hqs1/EPD_clock/MCU_Project/BSP/EPD/imagedata.c

#include "imagedata.h"

const unsigned char INIT_IMAGE_DATA[] = 
{
0xFF,0xFF,0xFF,0xFF,0xFF,0xFF,0xFF,0xFF,0xFF,0xFF,0xFF,0xFF,0xFF,0xFF,0xFF,0xFF,
0xFF,0xFF,0xFF,0xFF,0xFF,0xFF,0xFF,0xFF,0xFF,0xFF,0xFF,0xFF,0xFF,0xFF,0xFF,0xFF,
0xFF,0xFF,0xFF,0xFF,0xFF,0xFF,0xFF,0xFF,0xFF,0xFF,0xFF,0xFF,0xFF,0xFF,0xFF,0xFF,
0xFF,0xFF,0xFF,0xFF,0xFF,0xFF,0xFF,0xFF,0xFF,0xFF,0xFF,0xFF,0xFF,0xFF,0xFF,0xFF,
0xFF,0xFF,0xFF,0xFF,0xFF,0xFF,0xFF,0xFF,0xFF,0xFF,0xFF,0xFF,0xFF,0xFF,0xFF,0xFF,
0xFF,0xFF,0xFF,0xFF,0xFF,0xFF,0xFF,0xFF,0xFF,0xFF,0xFF,0xFF,0xFF,0xFF,0xFF,0xFF,
0xFF,0xFF,0xFF,0xFF,0xFF,0xFF,0xFF,0xFF,0xFF,0xFF,0xFF,0xFF,0xFF,0xFF,0xFF,0xFF,
0xFF,0xFF,0xFF,0xFF,0xFF,0xFF,0xFF,0xFF,0xFF,0xFF,0xFF,0xFF,0xFF,0xFF,0xFF,0xFF,
0xFF,0xFF,0xFF,0xFF,0xFF,0xFF,0xFF,0xFF,0xFF,0xFF,0xFF,0xFF,0xFF,0xFF,0xFF,0xFF,
0xFF,0xFF,0xFF,0xFF,0xFF,0xFF,0xFF,0xFF,0xFF,0xFF,0xFF,0xFF,0xFF,0xFF,0xFF,0xFF,
0xFF,0xFF,0xFF,0xFF,0xFF,0xFF,0xFF,0xFF,0xFF,0xFF,0xFF,0xFF,0xFF,0xFF,0xFF,0xFF,
0xFF,0xFF,0xFF,0xFF,0xFF,0xFF,0xFF,0xFF,0xFF,0xFF,0xFF,0xFF,0xFF,0xFF,0xFF,0xFF,
0xFF,0xFF,0xFF,0xFF,0xFF,0xFF,0xFF,0xFF,0xFF,0xFF,0xFF,0xFF,0xFF,0xFF,0xFF,0xFF,
0xFF,0xFF,0xFF,0xFF,0xFF,0xFF,0xFF,0xFF,0xFF,0xFF,0xFF,0xFF,0xFF,0xFF,0xFF,0xFF,
0xFF,0xFF,0xFF,0xFF,0xFF,0xFF,0xFF,0xFF,0xFF,0xFF,0xFC,0x03,0xFF,0xFF,0xFF,0xFF,
0xFF,0xFF,0xFF,0xFF,0xFF,0xFF,0xFF,0xFF,0xFF,0xFF,0xF8,0x01,0xFF,0xFF,0xFF,0xFF,
0xFF,0xFF,0xFF,0xFF,0xFF,0xFF,0xFF,0xFF,0xFF,0xFF,0xF0,0x00,0xFF,0xFF,0xFF,0xFF,
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
0xFF,0xF8,0x00,0x00,0x38,0xE3,0x8E,0x38,0xE3,0x8E,0x38,0xE0,0x00,0x00,0xFF,0xFF,
0xFF,0xF8,0x00,0x00,0x38,0xE3,0x8E,0x38,0xE3,0x8E,0x38,0xE0,0x00,0x00,0xFF,0xFF,
0xFF,0xFF,0xFF,0xFF,0xF8,0x1C,0x00,0x38,0xE3,0x8E,0x07,0xFF,0xFF,0xFF,0xFF,0xFF,
0xFF,0xFF,0xFF,0xFF,0xF8,0x1C,0x00,0x38,0xE3,0x8E,0x07,0xFF,0xFF,0xFF,0xFF,0xFF,
0xFF,0xFF,0xFF,0xFF,0xF8,0x1C,0x00,0x38,0xE3,0x8E,0x07,0xFF,0xFF,0xFF,0xFF,0xFF,
0xFF,0xFF,0xE3,0x81,0xC0,0xFF,0xF0,0x07,0x00,0x70,0x00,0xE3,0xF1,0xF8,0xFF,0xFF,
0xFF,0xFF,0xE3,0x81,0xC0,0xFF,0xF0,0x07,0x00,0x70,0x00,0xE3,0xF1,0xF8,0xFF,0xFF,
0xFF,0xFF,0xE3,0x81,0xC0,0xFF,0xF0,0x07,0x00,0x70,0x00,0xE3,0xF1,0xF8,0xFF,0xFF,
0xFF,0xF8,0x1F,0x80,0x38,0xFF,0x8E,0x00,0x1F,0x80,0x00,0x1F,0xF1,0xFF,0xFF,0xFF,
0xFF,0xF8,0x1F,0x80,0x38,0xFF,0x8E,0x00,0x1F,0x80,0x00,0x1F,0xF1,0xFF,0xFF,0xFF,
0xFF,0xF8,0x1F,0x80,0x38,0xFF,0x8E,0x00,0x1F,0x80,0x00,0x1F,0xF1,0xFF,0xFF,0xFF,
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

};
